dcvappliedtechnologyllc/PUBLIC/CAD/previews/dock_keel_v9_section.png

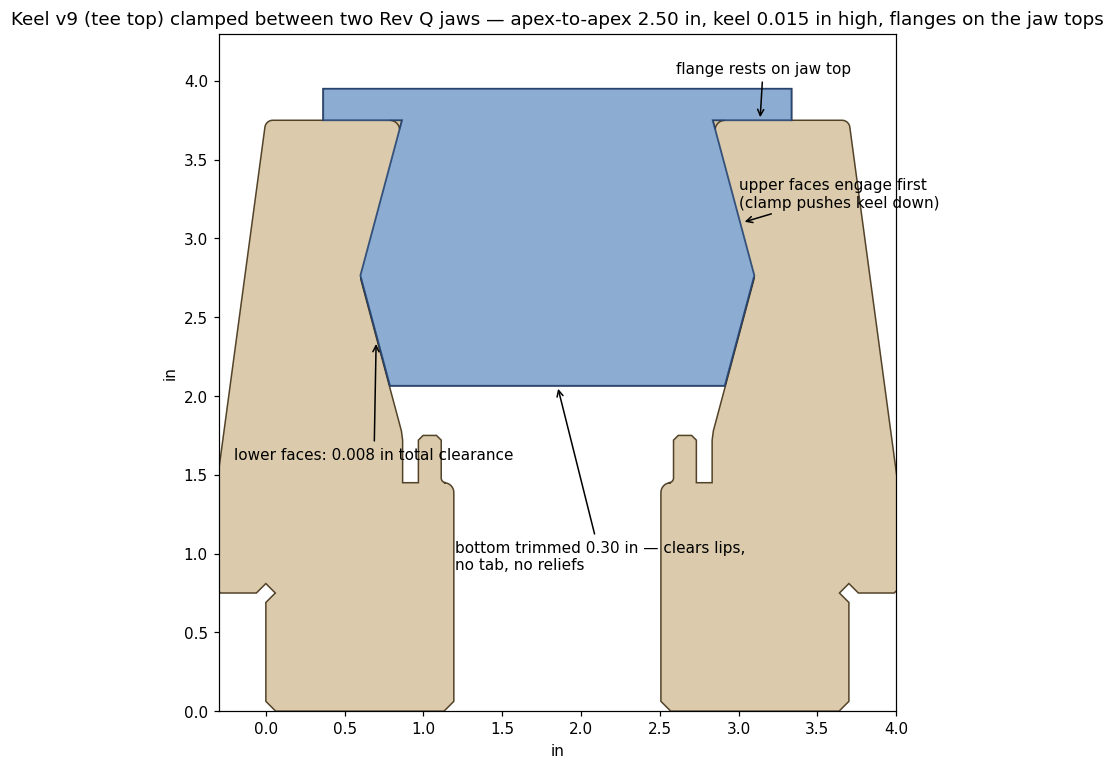
CAD/previews/dock_keel_v9_section.png
