dcvappliedtechnologyllc/PUBLIC/CAD/previews/dock_v3_clamp_section.png

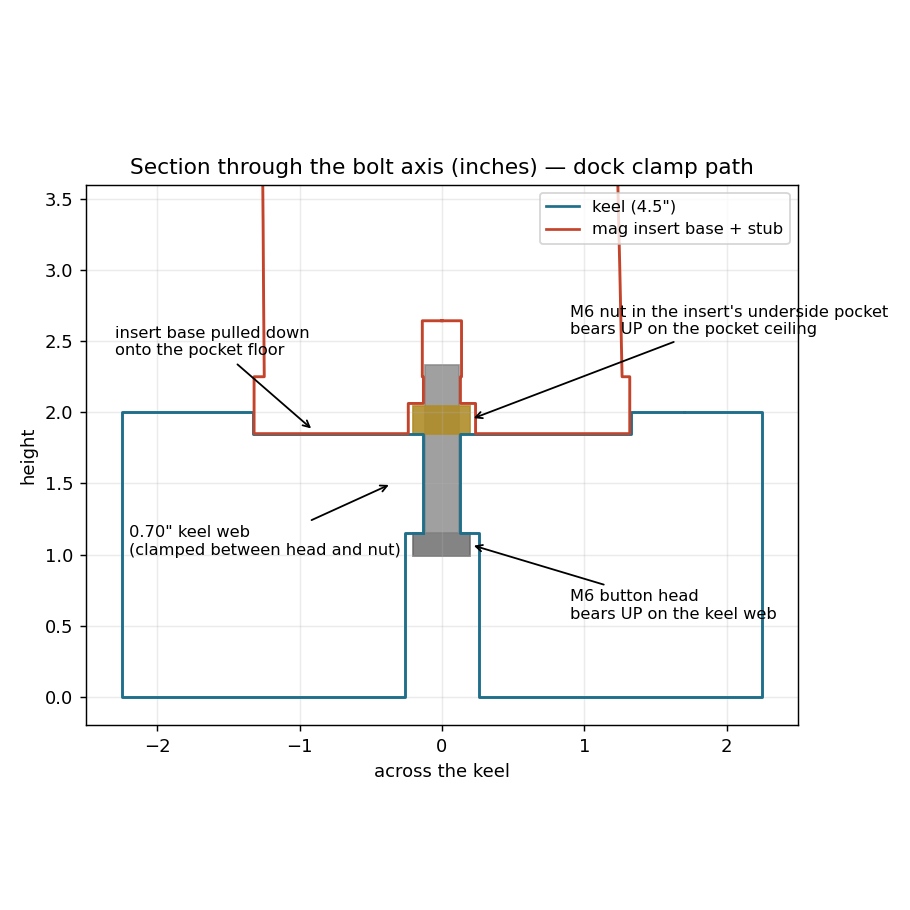
CAD/previews/dock_v3_clamp_section.png
