dcvappliedtechnologyllc/PUBLIC/CAD/previews/handwheel_B_ribs.png

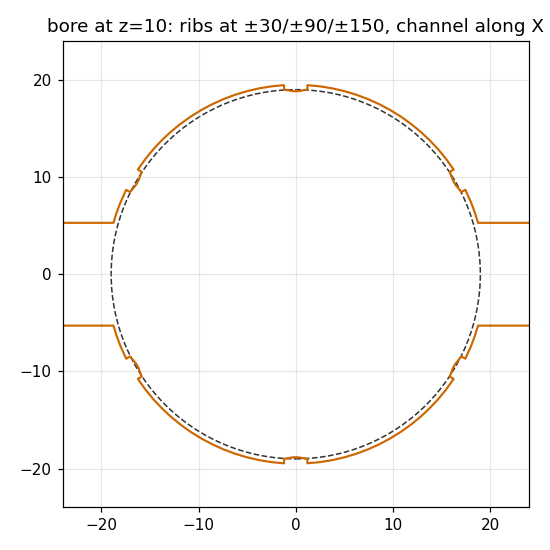
CAD/previews/handwheel_B_ribs.png
