dcvappliedtechnologyllc/PUBLIC/CAD/previews/handwheel_C_view.png

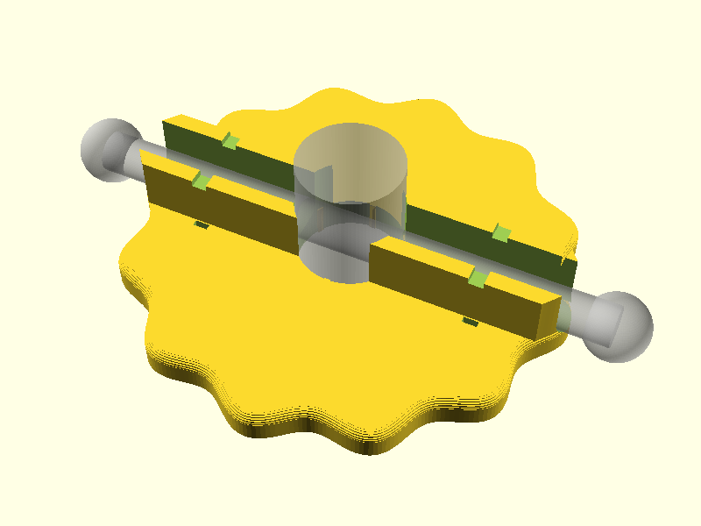
CAD/previews/handwheel_C_view.png
