dcvappliedtechnologyllc/PUBLIC/CAD/previews/jaw_plate_S.png

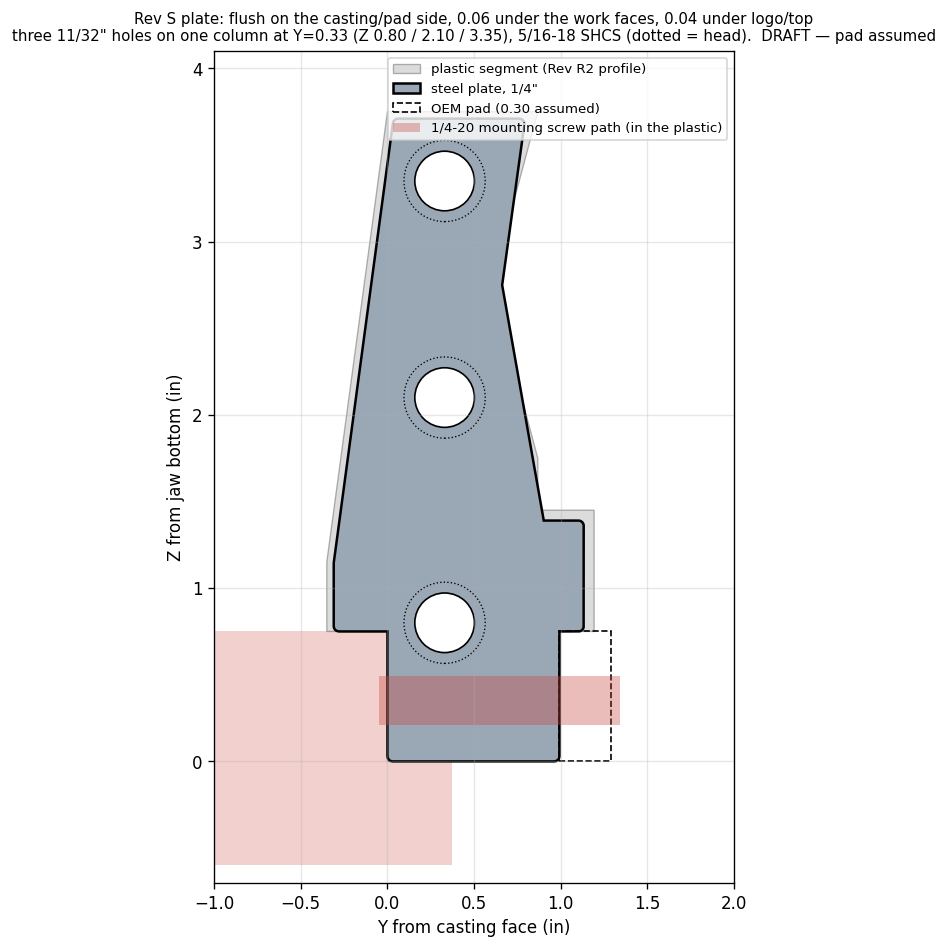
CAD/previews/jaw_plate_S.png
