dcvappliedtechnologyllc/PUBLIC/CAD/previews/jaw_revI_slot_profile.png

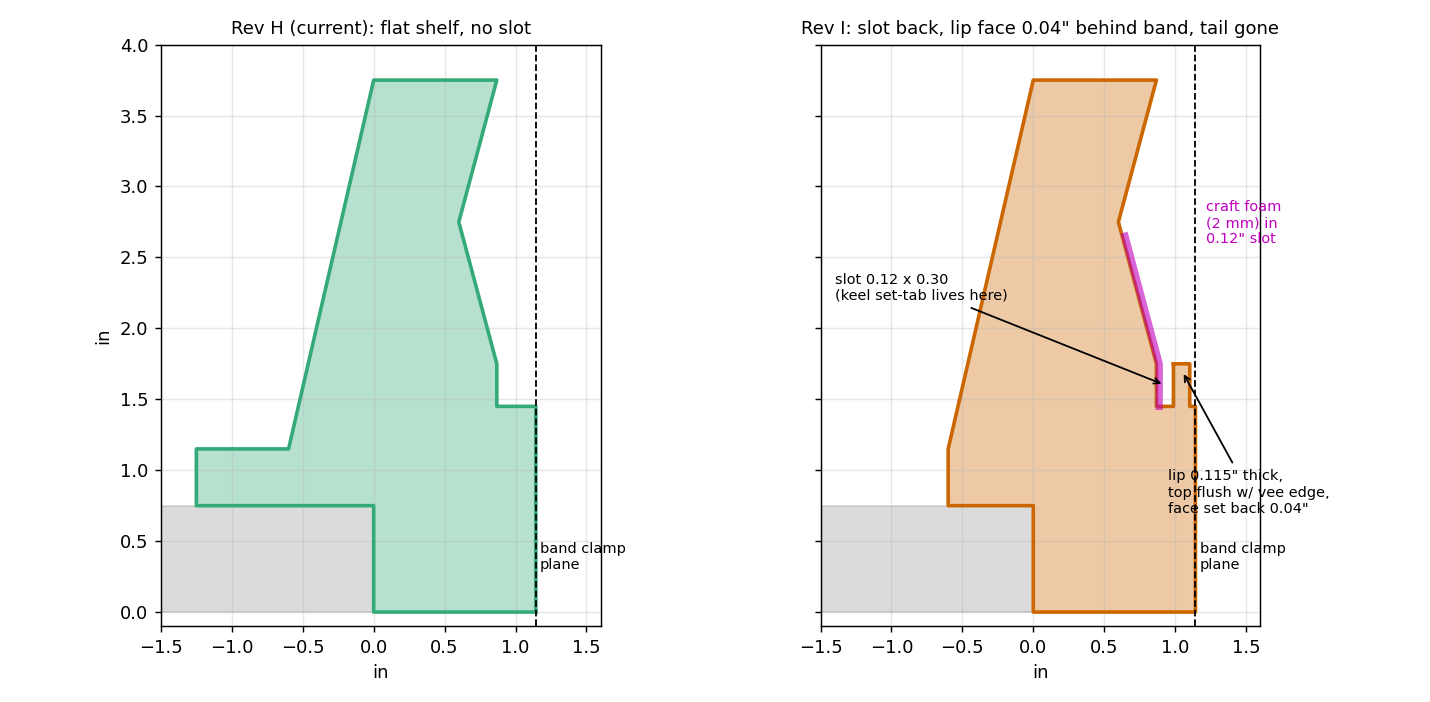
CAD/previews/jaw_revI_slot_profile.png
