dcvappliedtechnologyllc/PUBLIC/CAD/previews/jaw_revJ_public_views.png

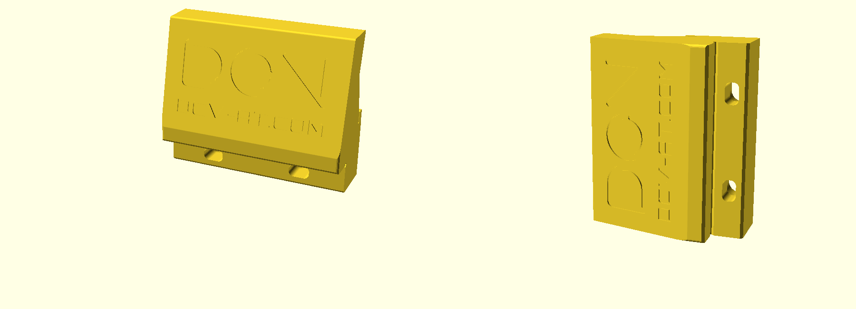
CAD/previews/jaw_revJ_public_views.png
