dcvappliedtechnologyllc/PUBLIC/CAD/previews/jaw_revJ_vs_I_section.png

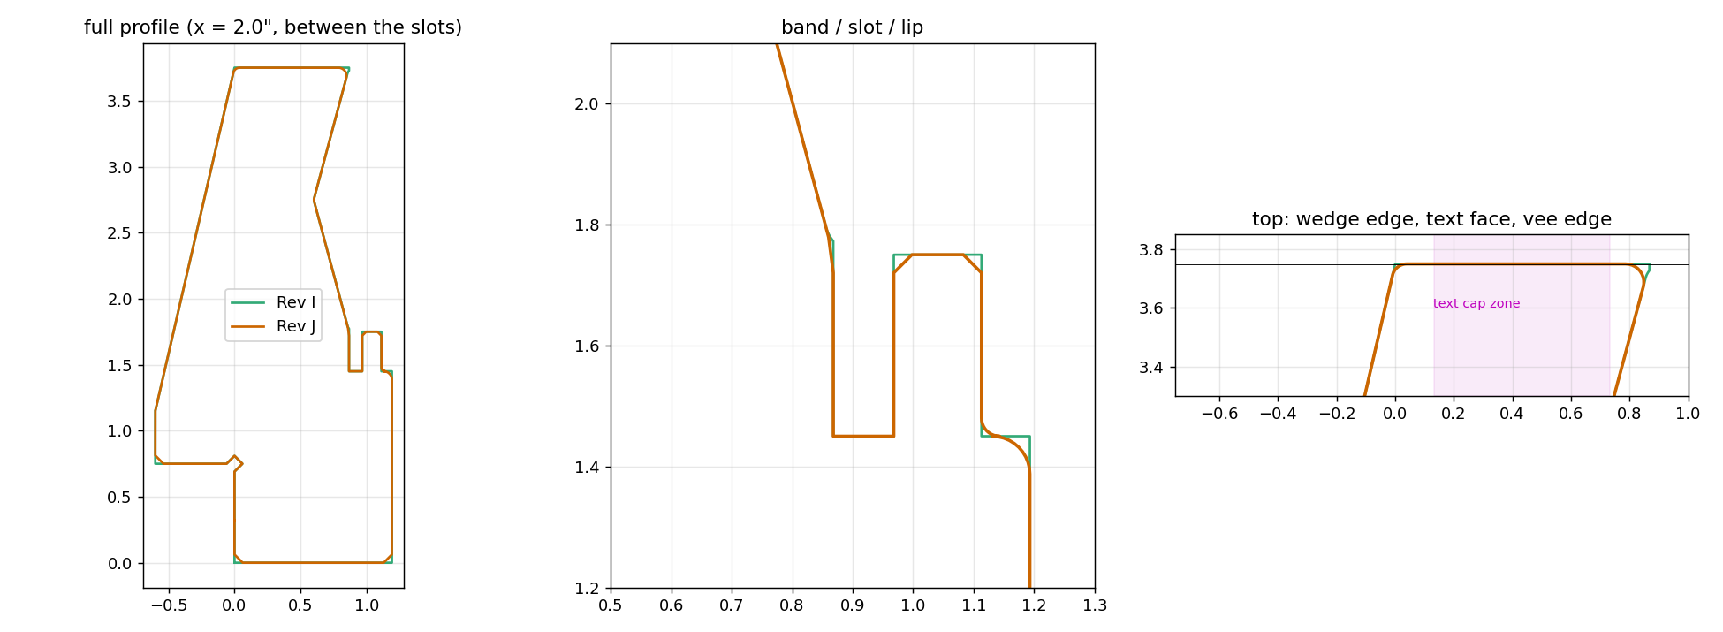
CAD/previews/jaw_revJ_vs_I_section.png
