dcvappliedtechnologyllc/PUBLIC/CAD/previews/jaw_revM_check.png

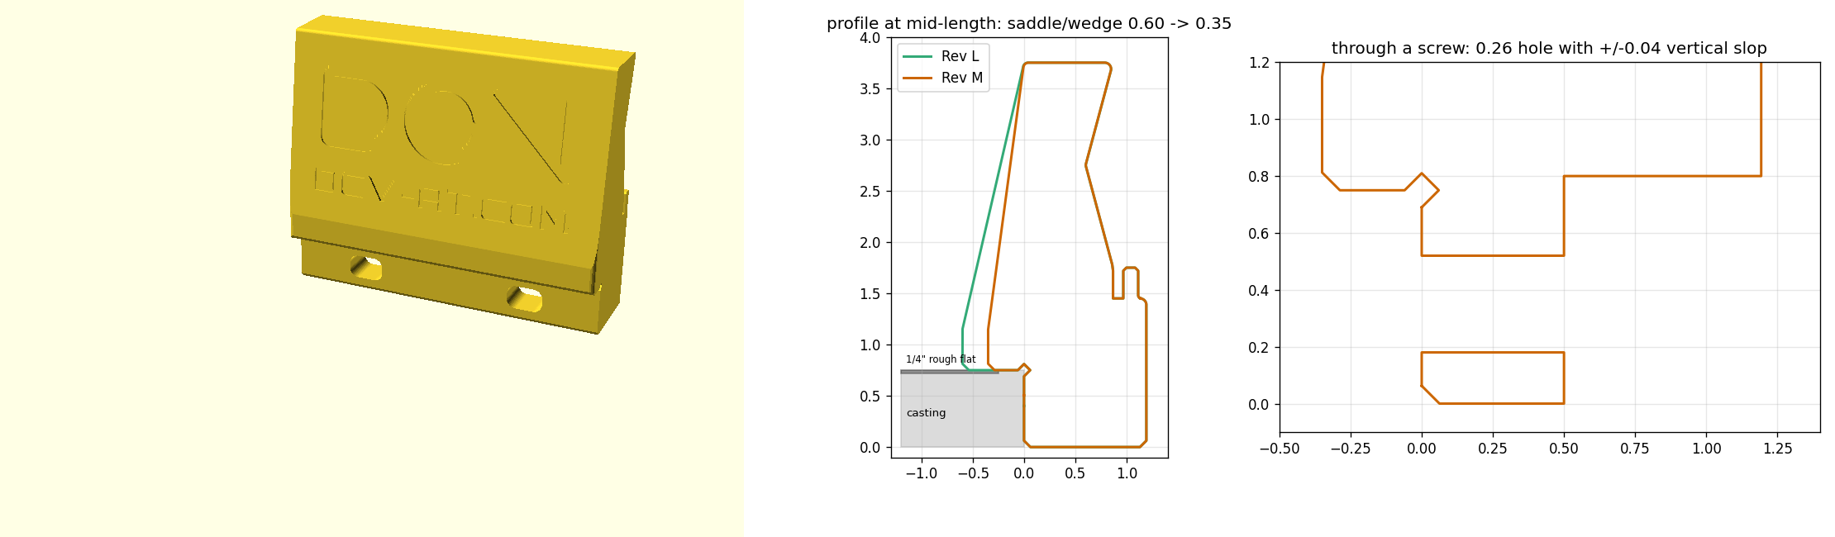
CAD/previews/jaw_revM_check.png
