dcvappliedtechnologyllc/PUBLIC/CAD/previews/jaw_revP_screw.png

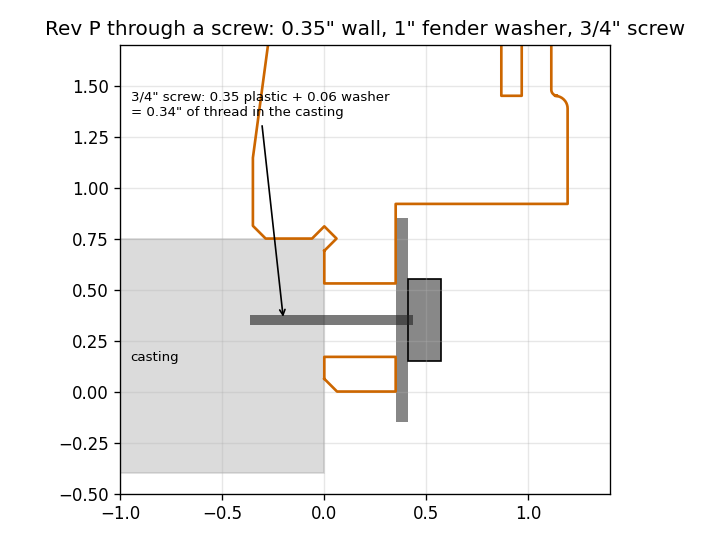
CAD/previews/jaw_revP_screw.png
