dcvappliedtechnologyllc/PUBLIC/CAD/previews/jaw_revQ_pockets.png

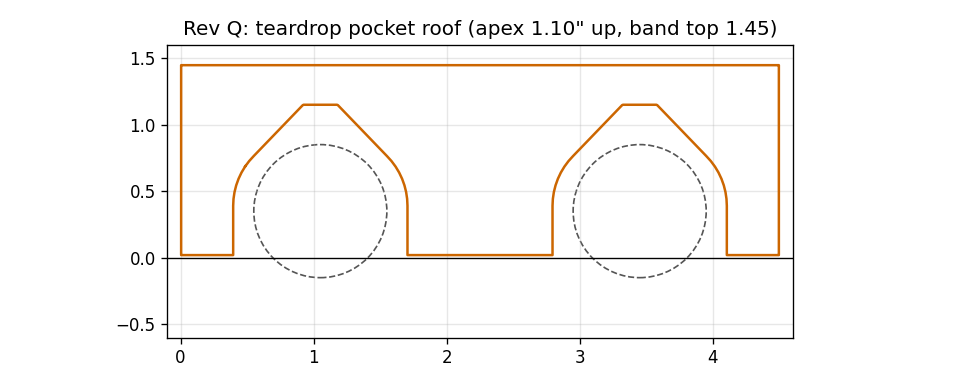
CAD/previews/jaw_revQ_pockets.png
