dcvappliedtechnologyllc/PUBLIC/CAD/previews/jaw_revR2_pocket_roof.png

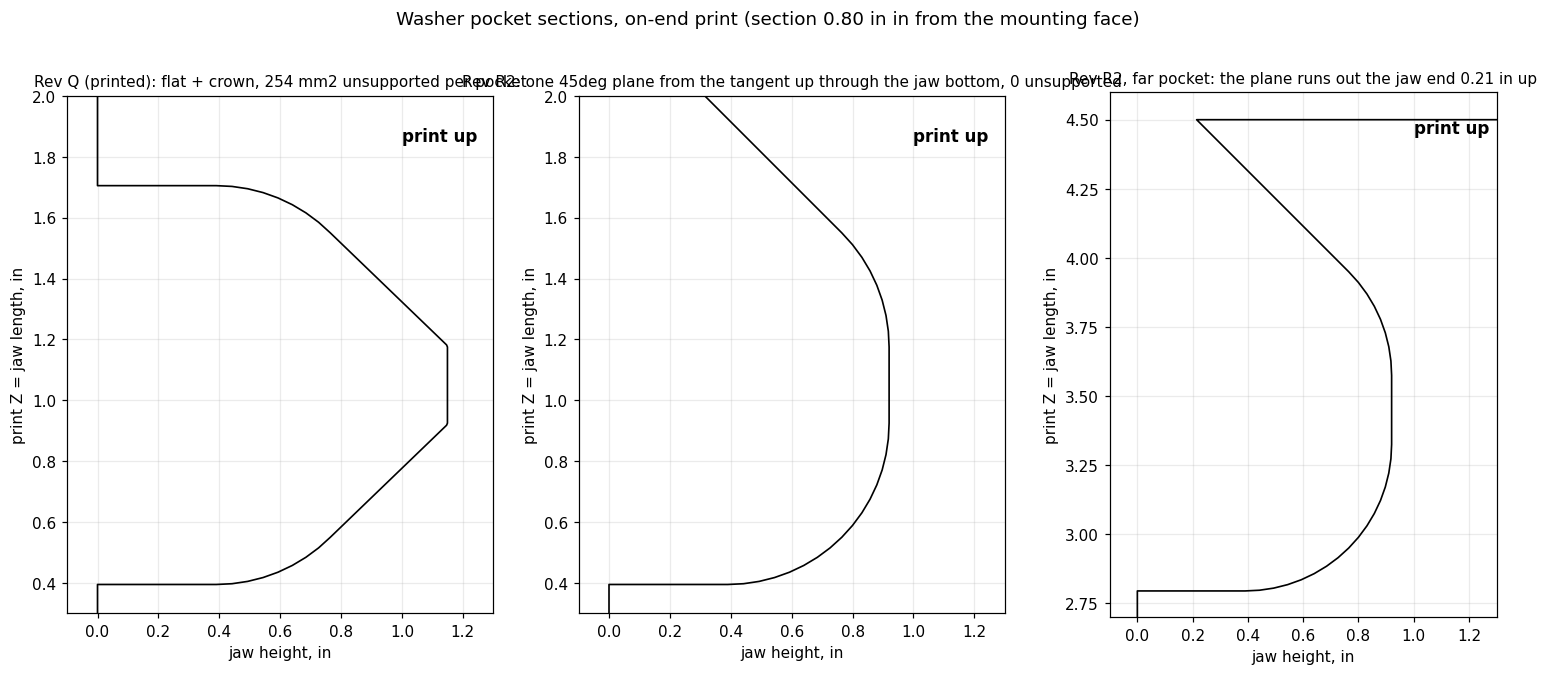
CAD/previews/jaw_revR2_pocket_roof.png
