dcvappliedtechnologyllc/PUBLIC/CAD/previews/jaw_S_chunk_preview.png

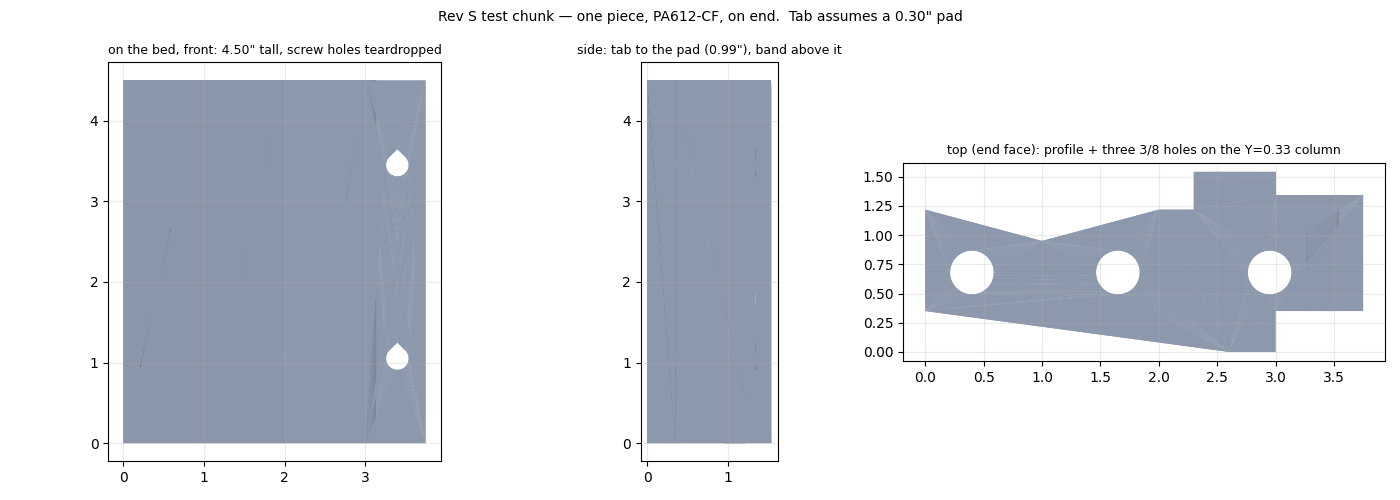
CAD/previews/jaw_S_chunk_preview.png
