dcvappliedtechnologyllc/PUBLIC/CAD/previews/rod_clamshell_A_layout.png

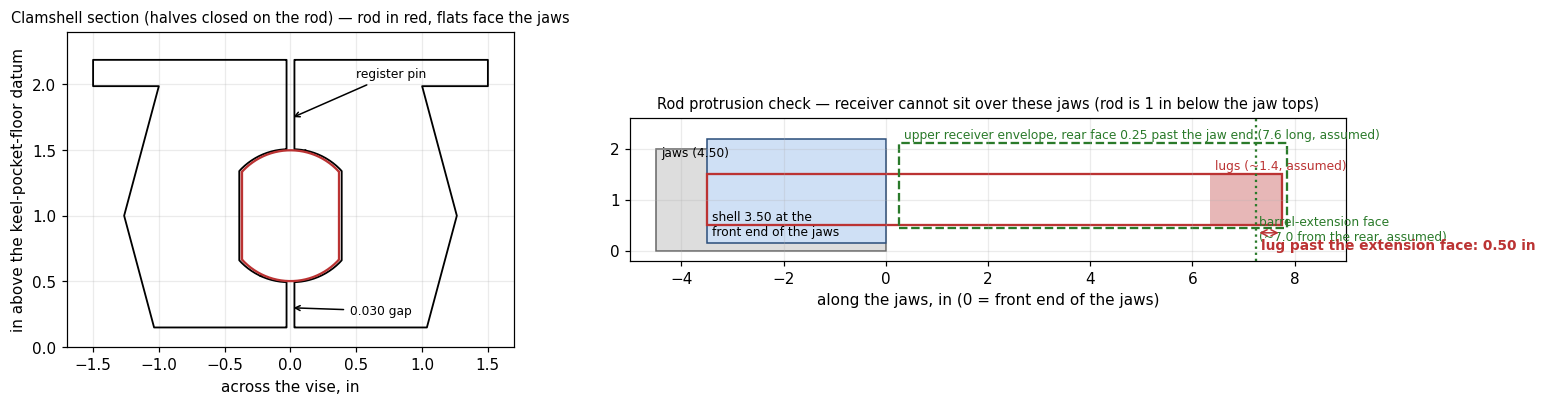
CAD/previews/rod_clamshell_A_layout.png
