dcvappliedtechnologyllc/PUBLIC/CAD/previews/vise_handwheel_E_face.png

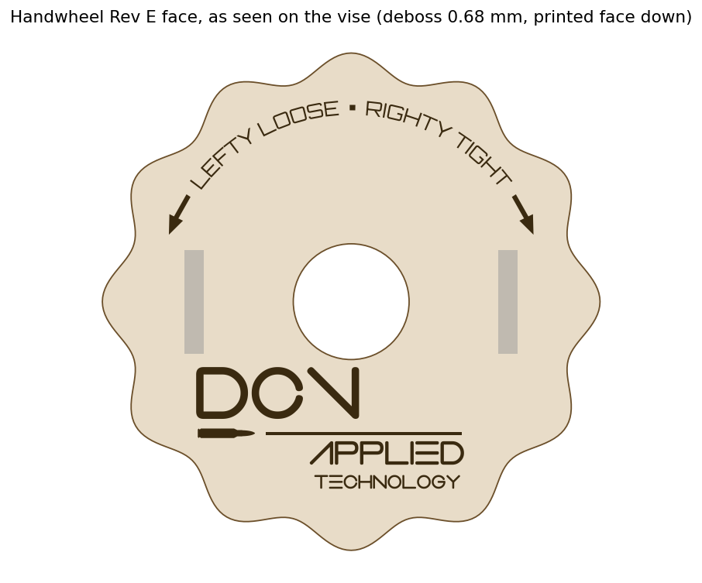
CAD/previews/vise_handwheel_E_face.png
