dcvappliedtechnologyllc/PUBLIC/CAD/Doyle Jaws 4.5in J - claude PETG+ proto.3mf

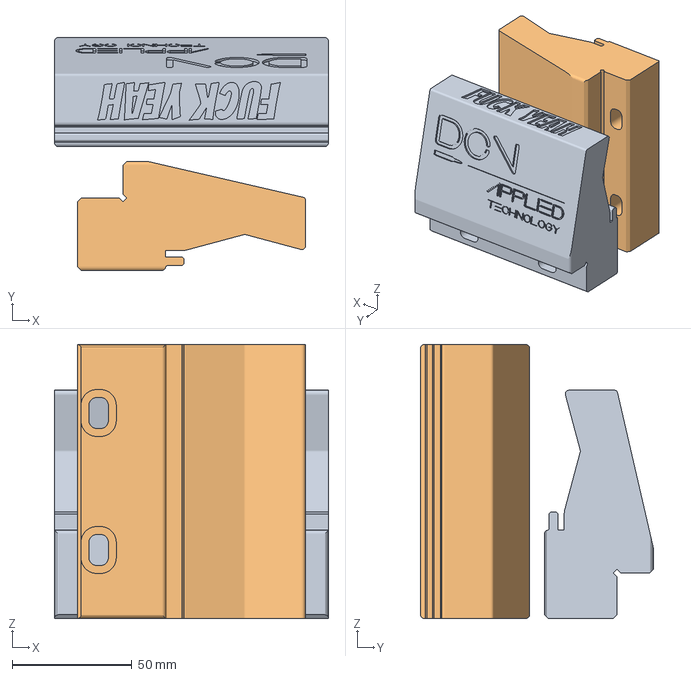
[picture p34: CAD file, 2026-09-08]
CAD/Doyle Jaws 4.5in J - claude PETG+ proto.3mf
114.3 x 97.2 x 114.3 mm
jaw_4.5in_J_DCV_movable_UPRIGHT_PRINT.stl
jaw_4.5in_J_plain_ONEND_PRINT.stl
