dcvappliedtechnologyllc/PUBLIC/CAD/vise_handwheel_C_PRINT.stl

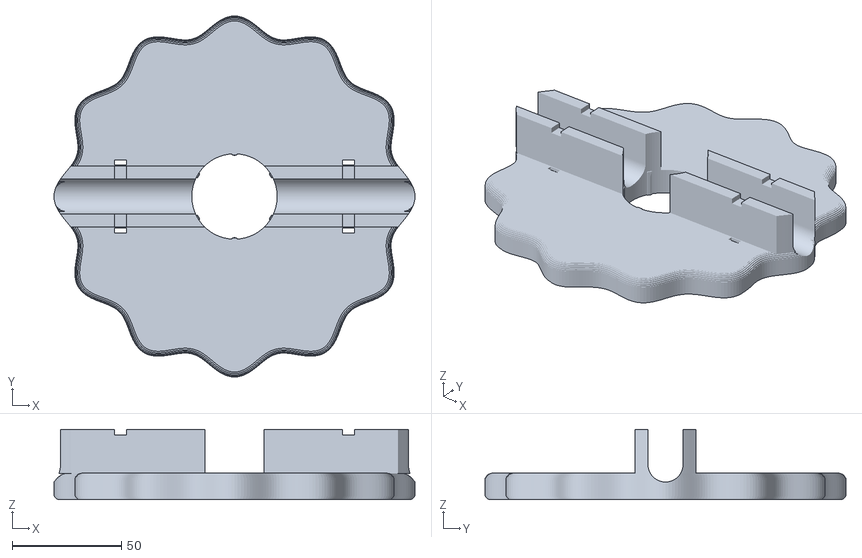
[picture p35: CAD file, 2026-09-08]
CAD/vise_handwheel_C_PRINT.stl
165.0 x 165.0 x 32.0
