dcvappliedtechnologyllc/PUBLIC/CAD/previews/dock_keel_v8_tab_fix.png

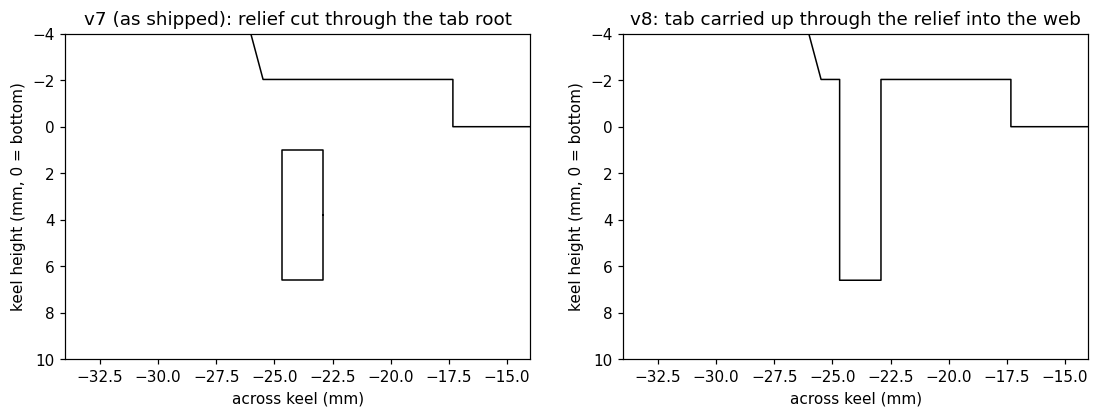
CAD/previews/dock_keel_v8_tab_fix.png
